harrydg1/ha-alarm-clock/Pictures/signal-2025-02-15-10-02-39-927.jpg

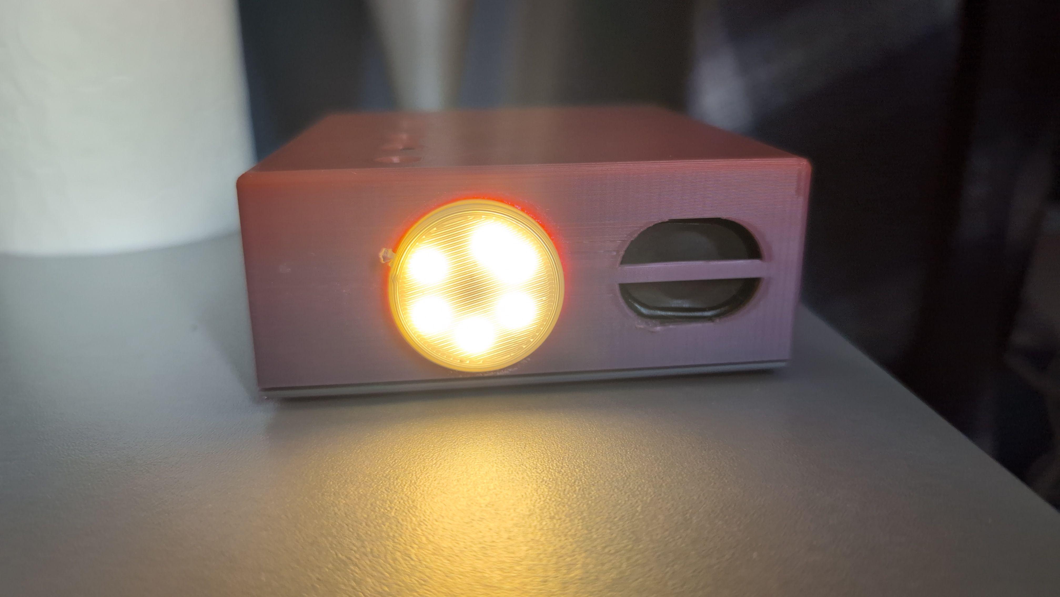
Pictures/signal-2025-02-15-10-02-39-927.jpg
