harrydg1/ha-alarm-clock/Pictures/signal-2025-02-15-10-03-19-373.jpg

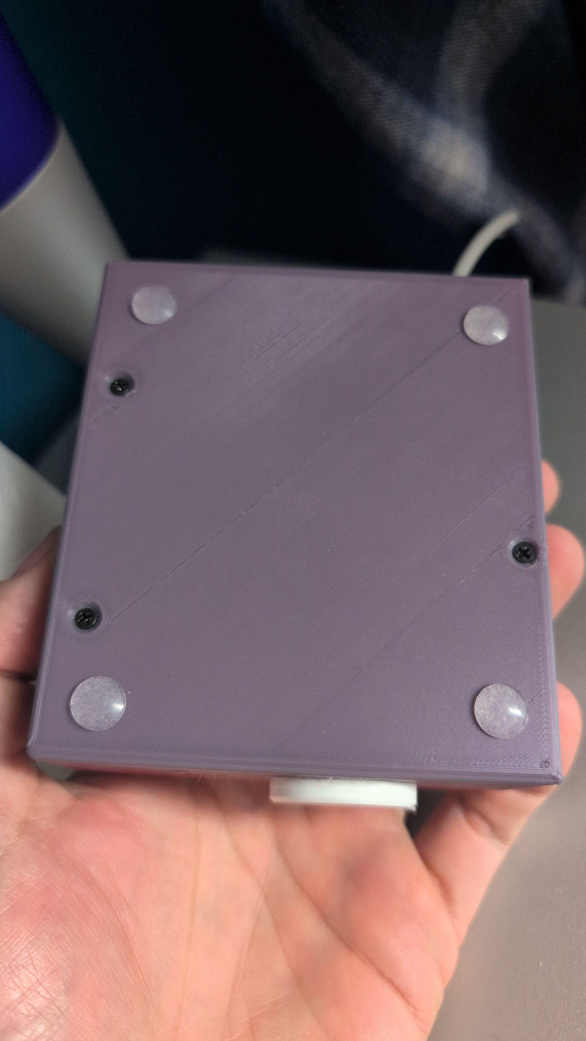
Pictures/signal-2025-02-15-10-03-19-373.jpg
